realRurichan/Ruri-Passport/hardware/review/procurement-bound-status.md

# 当前采购绑定与样板输出状态

2026-09-27：完整源工程已导出至 manufacturing/latest/Ruri-Passport-RevA.epro2，当前 Gerber 已重新生成并一致性复核。PCB DRC 0；163 元件/354 引脚核对 0；57 BOM 组/144 CPL 位号匹配。原理图仍有三组供应商属性警告，已通过有效规格属性审核解释；不是零警告。

可提交裸板打样/工厂 DFM。全贴片供料未闭环：MIC1/J2/J3 当前为邮寄供料，麦克风自动替代料未核准。报价已知约 586.13/套仍缺项，非最低价。详细状态、限制和哈希见 ../manufacturing/latest/README.md、quote.md、manifest.json。
