realRurichan/Ruri-Passport/hardware/design/DISPLAY.md

# CL40BC264-40C 非触摸屏

用户指定 CL40BC264-40C 的 Without RTP 版本，替代此前所有候选。此前误传的 CL24CK229-18A 不采用。用户已接受 PCB 调整为 88 × 135 mm。

资料：用户提供的 `CL40BC264-40C_RTP&WithoutTP.rar` 中 `CL40BC264-40C_SPEC_V0 鸿讯电子.pdf`（第 3–9 页）及 `CL40BC264-40C接线图.pdf`。已核对非触摸机械图与四线 SPI 接线图；厂商原始文件和示例代码未复制入开源仓库。

2026-09-26 已在客户端保存 SPI 接线；PCB 尚未同步。原理图自定义符号仍有旧并口功能别名，连接以引脚编号及外部网络标签为准，别名整理待完成。

## 已确认参数

| 参数 | 数值 |
| --- | --- |
| 对角线 / 分辨率 | 4.0 英寸 / 320 × 480 |
| 驱动 IC | ILI9488 |
| 显示区 | 55.68 × 83.52 mm |
| 模组外形 | 60.88 × 94.57 mm |
| 非触摸版厚度 | 2.48 ± 0.15 mm，不含双面胶 |
| 排线 | 40 pin，0.5 mm 间距；端部宽 20.50 mm |
| 插入端厚度 | 0.30 ± 0.05 mm（FPC + PI） |
| 视角方向 | 12 点钟方向；不将其标为 IPS |
| 接口选择 | 四线 8 位 SPI，IM0=1、IM1=1、IM2=1 |
| VCC / IOVCC | 接线图采用 3.3 V；规格表正常工作上限 3.3 V，最终电源需计入容差 |
| 背光 | 8 颗白光 LED 并联；正向压降 2.9 / 3.1 / 3.3 V（最小/典型/最大） |

厚度不能用规格书第 3 页带 RTP 的 3.62 mm。现有 PCB 文档层 60.88 × 94.57 mm 包络可作近似包络，但未包含 FPC 折弯、连接器、装配公差和禁布区，不是最终机械封装。

## 40 pin 接口分配

| 屏幕针脚 | 屏幕信号 | 计划连接 |
| --- | --- | --- |
| 1–4 | XL / YU / XR / YD | 非触摸版本不连接 |
| 5、16、37 | GND | GND |
| 6 | IOVCC | 显示 I/O 电源，3V18_PERIPH |
| 7 | VCC | 显示电源，3V18_PERIPH |
| 8 | FMARK / TE | 本版暂不接，保留调试焊盘方向 |
| 9 | CS | LCD_CS_N / GPIO10 |
| 10 | RS | LCD_DC / GPIO9 |
| 11 | WR / SPI_SCL | LCD_SCK / GPIO8 |
| 12 | RD | 写入模式固定为高电平（IOVCC），不能悬空 |
| 13 | SPI_SDA | LCD_MOSI / GPIO16 |
| 14 | SPI_SDO | 不连接 |
| 15 | RESET | LCD_RESET_N，GPIO 扩展器控制；R5下拉，默认复位 |
| 17–24 | DB0–DB7 | 按厂商四线 SPI 图接 GND |
| 25–32 | DB8–DB15 | 按厂商四线 SPI 图接 GND |
| 33 | LEDA | 背光驱动输出，禁止直接接 MCU GPIO |
| 34–36 | LEDK | 三脚接同一背光阴极网络，经限流/驱动回路 |
| 38、39 | IM0、IM1 | IOVCC |
| 40 | IM2 | IOVCC |

GPIO43 分配 LCD_BL_PWM，用于控制背光驱动。Display.esch2 已绘制接口符号、模式配置、去耦、CS 上拉和 RESET 下拉。J1 已关联 FH12A-40S-0.5SH(55) 候选封装，Optics页已加入TLV9001+AO3400A恒流背光草稿，电源已加入Power页；不能当作制造网表。

## 背光和装配待办

- 第 5 页背光电流表的 160 / 200 mA 应结合原页列位置及供应商确认典型/最大值；暂按 200 mA 预留驱动和热预算，不据此承诺续航。
- 接线图用 3.3 V + 2.2 Ω 限流作示例。这不是恒流方案，不能据此保证电流；需按电源容差、LED 压降和实测选择 PWM 背光电路。
- 40 pin / 0.5 mm / 0.3 mm 只是连接器筛选条件。用户确认上接触；仍需复核锁扣方向、焊盘编号和最终折弯方向，再确定采购型号与 PCB 封装。
- 确认非触摸订货选项、单价与供应情况。未下单、未核价。

## J1 上接触座候选封装

型号 FH12A-40S-0.5SH(55)，原厂明确 FH12A 为上接触翻盖式。依据 [Hirose FH12 官方目录](https://www.hirose.com/product/document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) 本次下载版第 6、10 页建候选封装（目录版本页码可能不同）。

- 信号焊盘 40 个，0.5 mm 间距，0.30 × 1.30 mm，首末中心距 19.5 mm。
- 两个固定焊盘各 1.8 × 2.2 mm，横向中心 ±11.65 mm；相对信号焊盘中心线朝插入口方向 3.25 mm。固定焊盘不接信号。
- 以插入口朝 PCB 局部正 Y 的俯视图编号，1 脚置于局部 X=+9.75 mm；这是图纸解释，仍须对照独立料号图和实际排线复核，尚未生产签核。
- J1 暂放在 PCB (49,59) mm，位置随当前屏幕包络调整，用于验证折回排线方案，并非最终装配签核。
- 尚未完成钢网开口、阻焊、公差、丝印、装配间隙或 DRC 检查；嘉立创供料和价格未确认。不得把其他同针数连接器直接替换。
