realRurichan/Ruri-Passport/hardware/design/BATTERY.md

# 电池选型：VP505060 成品包候选

2026-09-26。首选孚赛能源 VCELL **VP505060** 的单节保护电池包，要求定制三线 NTC 与项目连接器。电芯规格方向已选定，成品包采购型号尚未冻结：公开页没有两只样品价格、起订量及该 NTC/线束配置的订单号。

## 厂家公开参数

| 项目 | VP505060 |
| --- | --- |
| 标称电压 / 容量 | 3.7 V / 2000 mAh，7.4 Wh |
| 充满电压 | 4.2 V |
| 最大持续放电 | 1.5C，即 3 A；不是峰值电流 |
| 最大充电电流 | 1C，即 2 A |
| 尺寸 | 厚 5.0 × 宽 50.5 × 长 62.5 mm，公开页称最大值、包含 PCM |
| 重量 | 约 34 g |
| 充电温度 | 0–45 °C |
| 定制选项 | 保护板、线材、插头、NTC |

依据：[VCELL 原厂产品页](https://www.vcellpower-battery.com/zh_cn/3.7v/505060-3-7v-2000mah-lithium-rechargeable-battery-with-pcm.html)。以上是公开参数，须以供应商确认的成品包规格书为准；网页没有证明任意保护板和插头版本均可连续输出 3 A。

## 与本项目的匹配

机械预留区为 x=6…71、y=40…100 mm，即 65×60 mm。把电池长边沿板 X 方向放置，62.5×50.5 mm 可放入该区域；拟定位 x=7.5…70、y=44…94.5 mm。这是平面包络筛查，NTC、绝缘胶、焊接折边及出线弯曲后的成品最大尺寸仍需供应商图纸；壳体需另外预留安装公差和厂家规定的膨胀空间，不能夹紧软包。三线约 80 mm 作为样品线长目标，最终长度按装配图确定。

现有功率分配以 3.18 V / 1.7 A、85%估算效率为基准，电池/VSYS=3.3 V时约2.14 A，若VSYS=2.8 V则约2.48 A（均含背光/IR约0.21 A）。3 A候选有设计余量，但效率、低电量压降和实际电流仍需样板验证。

**J3 已改为 3 A 接口：** JST S3B-XH-SM4-TB(LF)(SN)，采购编号 C161860，三针卧式贴片，XH 系列实际间距 **2.50 mm**。匹配线端外壳 XHP-3、端子 SXH-001T-P0.6；正负极功率线用 **22 AWG**，厂家 3 A 额定以该线径为条件。PH2.0 插头不兼容。针序按下方针号核对。PCB、原理图和 Gerber 已同步，严格 PCB DRC 为 0 错误；整机最大持续电流仍需样板验证。[JST XH 原厂规格](https://www.jst-mfg.com/product/pdf/eng/eXH.pdf)。

温度匹配尚需完成：候选电池规定充电 0–45 °C，BQ24074 配推荐 103AT-2 的原生窗口约 0–50 °C；不能据此认定完全匹配。电池成品包必须具备符合电芯要求的充电温度保护，或在量产前调整板端温度门限并验证。

## 成品包采购要求

- 1S 3.7 V、4.2 V充满、约2000 mAh；电芯、PCM、功率导线及最终插头均满足至少3 A连续能力，并提供过流保护阈值/延时。保护板过流触发电流不等于连续额定电流。
- 保护板具备过充、过放、过流、短路保护。采购必须包含保护板，不买裸电芯直接接板。
- 贴附电芯的 NTC：R25=10kΩ，优先103AT-2或经曲线核对的等效件，B25/85=3435K，阻值和B值公差按±1%要求；另一端接成品包P−。不能用第三根ID/数据线替代NTC。[SEMITEC参数](https://www.semitec-global.com.cn/products/thermistor_at/)、[TI BQ24074推荐103AT-2](https://www.ti.com/lit/ds/symlink/bq24074.pdf)。
- 当前电路的J3功能顺序：1=P+/VBAT，2=NTC/BAT_NTC，3=P−/GND。插头壳采用 XHP-3；以带针号的图纸核对，不以红白黑线色或所谓正反插头名称替代针号。
- 两只样品，供应商确认最小起订量、成品包全尺寸、放电曲线、样品单价、含税/运费及交期。尚无实际报价，不计入已核准整机成本。

## 未入选方向

普通仅写505060/2000mAh的通用电池不能自动等同VP505060；例如[亿莱505060](https://www.yilaipower.com/battery/fully-certified-505060-2000mah-3.7v-rechargeable-li-po-battery.html)公开持续放电仅1C（2 A），达不到当前3 A采购目标。103450通常更厚，本项目优先5 mm级软包，避免增加机身厚度。

## 可复制给商家的询问文本（尚未发送）

需要2只VP505060单节3.7V/2000mAh保护锂聚合物电池，4.2V充满。要求电芯、保护板和线束连续放电≥3A，支持约0.5A充电，带贴附电芯的10kΩ±1%、B25/85=3435K±1% NTC，NTC另一端接保护输出P−。请提供成品包规格书、持续放电测试条件、保护阈值/延时、带NTC与线束的最大尺寸、起订量、2只样品单价和运费。线长暂按80mm，插头采用XHP-3，功率导线22AWG，端子SXH-001T-P0.6；1=P+、2=NTC、3=P−，按针号图确认后制作。不要用3.8V/4.35V高压电芯或两线版本替代。
