realRurichan/Ruri-Passport/hardware/design/MECHANICAL.md

# 88×135mm 布局草稿

2026-09-26用户同意板长从125mm增加至135mm，以天线净空和可用性为优先。下表为PCB左下角原点，单位mm，正Y向上。元件仍在布局，不是机械签核。

| 对象 | 拟定位置/外形 | 状态 |
| --- | --- | --- |
| PCB | x=0…88，y=0…135 | 原生板框已更新、读回确认 |
| 非触摸屏 | x=13.56…74.44，y=38.5…133.07 | 60.88×94.57；未计FPC与装配公差 |
| 后侧电池 | x=6…71，y=40…100 | VP505060 成品包候选，62.5×50.5×5 mm；三线NTC、线束、壳体余量待核准，见 BATTERY.md |
| ESP模组 | x约4…22，y约0…25.5，天线朝下 | 原生封装外形；需整机RF复核 |
| Wi-Fi天线周边 | 板内x=0…37，y=0…约21 | 已生成四铜层禁止导线、填充和铺铜区域，排除模组自身屏蔽/焊盘区 |
| NFC板载线圈 | x=53…87，y=1…25 | 34×24、4匝、0.4线宽/0.3间距初值；铜线与馈线已画入，整机调谐待完成 |
| 五向键中心 | UP(42,31)，DOWN(42,17)，LEFT(35,24)，RIGHT(49,24)，OK(42,24) | 7mm中心距，OK开关旋转90°避让焊盘；UP开关本体距屏幕外框约4.95mm。键帽外沿和装配公差待核查 |
| USB-C | 下边缘，中心x=44 | 座体/开口与焊盘待核对 |
| microSD | 右边缘，中心y约73 | 卡插拔包络待核对 |
| POWER | 右边缘，y约89 | 须检查伸出量与壳体行程 |
| M2 固定孔 | H1(3,132)、H2(84.5,132)、H3(3.5,38)、H4(84.5,50) | Ø2.2mm 非金属化孔，四层铜箔避让 Ø5.2mm；螺柱外径≤4.5mm，螺丝头直径≤4mm |

屏幕金属与NFC线圈上缘的平面间隔为13.5mm；这一间隔不能证明射频性能。按键、USB壳、电池线、螺丝柱和外壳金属也需纳入调谐。

屏下器件、背面电池、FPC折回、连接器插拔和声孔都未完成高度/实体干涉验证。J1暂移至(49,59)，仅随屏幕包络上移，FPC端部基准及上接触方向仍须确认，不能直接据此开外壳。

四铜层已启用。暂定单面SMT以控制贴片成本；最终叠层、板厚、阻抗和报价在布线及制造核查中落实。本尺寸不按10×10cm免费板预算。

MIC1 为板载底部声孔麦克风，库中有约 Ø0.4mm 通声孔；需在最终钻孔文件及外壳中确认畅通。扬声器采用 J5 外接 8Ω/≥1W 单元，实体和线束仍待选定。

后壳扬声器暂按 Ø28×5mm 安装包络，中心 (30,117)，位于电池占位上方；这只是装配空间预留，不代表已选定或核价的扬声器。麦克风通声孔中心约 (82.786,110)，后壳需单独声孔或声道，避免电池、泡棉和螺柱遮挡。

2026-09-26补充：用户要求扬声器以便宜、能响为主。候选兴华鑫20MM-8Ω1W-L60MM（C49246973），Ø20×4.2mm，保持现有较大包络；尚须配好PH2.0双针成品线束并确认国内两件价格，未冻结采购。电池仍未定型号，约2000mAh、保护板及NTC要求不变；见[审核与报价](../review/assembly-quote-20260926.md)。

用户于 2026-09-26 明确要求预留外壳固定孔。下方两个固定孔采用错位布局，避开 Wi-Fi/NFC 天线和电池占位；外壳底边还需绝缘支撑台阶，承接按键和 USB 插拔力。固定孔与螺柱区域位于屏幕外形左右两侧。H1 与红外接收器较近，按 Ø5.2mm 预留包络平面筛查，正式外壳设计仍须核对器件高度和装配公差。权威坐标见 `mounting-holes.json`。
