realRurichan/Ruri-Passport/hardware/review/usb-footprint-correction-20260926.md

# GCT USB4105 封装修正依据

2026-09-26。对原厂 USB4105 Rev B1 两页尺寸图与原生封装进行一次独立只读比较；随后按厂家推荐铜图修正。此记录不等同于生产放行。

- 原厂图：<https://datasheet.octopart.com/USB4105-GF-A-060-GCT-datasheet-192318489.pdf>。图纸覆盖 USB4105 系列的 shell stake 长度选项。
- 原型号 USB4105-GF-A 对应供应商候选 [C3020560](https://www.lcsc.com/product-detail/C3020560.html)，尚未确认国内贴片库与订单价格。
- PCB 以 USB 中心线 x=44 mm、板边 y=0 为基准，J2 原点 (44,4.973) mm。
- 16 个逻辑 SMD pad 保持原引脚/网络，宽 0.30、长 1.15、中心 y=7.355 mm；左右电源/地相邻 pad 边缘相接，等价于厂家四个 0.60 mm 合并铜区。
- 两定位孔恢复为 (41.11,6.28)、(46.89,6.28) mm，孔径 0.65 mm。没有缩孔或删除定位孔。
- 四个外壳槽 x=39.68/48.32 mm；前排 y=2.60，孔 0.60×1.40、铜 1.00×1.80；后排 y=6.78，孔 0.60×1.70、铜 1.00×2.10 mm。槽和铜均为纵向长圆。
- 手工锡膏图形同步目标铜图；厂家图的 solder area 不是已确认的钢网开孔/锡量规范，最终钢网仍须生产审核。
- 默认 stake 长度 S=0.95±0.15 mm 不是板厚要求；本图没有给出板厚上限/下限。短脚 PTH 的实际贴片/焊接工艺尚待确认。

修正后定位孔与最近焊盘的名义净距为 `hypot(0.01,0.50)-0.325 = 0.175100 mm`，大于现有 6 mil 电气间距规则，仍小于嘉立创常规 NPTH 0.20 mm 避铜要求。保留原规则，不设忽略项。最终钻孔、铜层和钢网导出核对及嘉立创 DFM 接受记录完成前，USB-1 制造项仍未关闭。

廉价候选 SHOU HAN TYPE-C16PIN2MD(073) / C2765186 未采用：库与厂家孔、焊盘及槽尺寸不一致，图纸另推荐 0.80 mm PCB；不能以其价格直接替换当前 1.6 mm 板方案。
