realRurichan/Ruri-Passport/hardware/review/power-review-20260926.md

# Power 方案独立审查

只读、单轮，2026-09-26。未读取旧 review；未改 EDA、源脚本或工程。检查 add_power.py、Power.esch2，并交叉读取 Controls 的实际网络；阅读 TI/ADI 原始资料。没有运行原生 ERC、测量实板或验证封装尺寸，因此以下是电气方案和源文件审查，不是放行结论。

**FIX FIRST：P1、P2、P4。P3 必须明确实现或记录为首版限制；已知 ESD/输入保护缺口仍未关闭。**

## P1 — SERIOUS：LTC2950 的 SD 安全关机时间不能靠 OFFT 延长

实际 U5=LTC2950CTS8-1，C17=330nF。INT 经 TCA9535 P06 通知主控；PB 没有更早的独立检测。约2.15秒按键时间过去后才产生 INT，此后自动切电时间最短只有800ms（典型1024ms）。软件真正拿到中断后还要付出 I²C、调度、停止应用、文件系统同步与卡内部忙时间。没有任何已验证的最长处理时间。任意 SD 卡和用户应用下，不能把它称为保证安全关机。增加 C17 只推迟 INT，不增加最后窗口。[ADI LTC2950，p3、p8–11](https://www.analog.com/media/en/technical-documentation/data-sheets/295012fd.pdf)

最小硬件修复：采用 **LTC2954-1 的 TS8**，针号1–8功能对应，7脚改名 PDT；其 INT 可在按下约32ms时报出，持续长按才由 PDT 强制切断。C17可改1µF，形成约6.4秒强制关机时间；核实容差后的最短时间。普通按键请求由系统完成同步/等待卡非忙，再通过 KILL 切断。强制关机仍要明确可损坏未完成写入，不能承诺任意卡无损。应重新核对精确料号、库与供货，不能仅在 BOM 中改字符串。[ADI LTC2954，p2、p9](https://www.analog.com/media/en/technical-documentation/data-sheets/2954fb.pdf)

## P2 — SERIOUS：没有电池低电量预警路径，保护板切断不是正常关机策略

实际可见信号只有 CHG、USB_PGOOD、PWR_INT；没有 VBAT 分压到 ADC、外部电量计或低电压比较器。TPS63802 会维持3V18直到低电压/电流条件无法满足；测3V18或其PG不能提前代表电芯余量。最终可能是电池保护板突然切断，SD 正在写入。电池保护器的实际门限和恢复条件还未确定。

最小修复：加一个独立于稳压输出判断的电池低电压监测，可用 I²C 电量计/ADC，或阈值与迟滞明确的低功耗比较器，输出给 TCA9535 剩余输入。设正常关机阈值高于保护阈值，并按电池压降与实际最大负载验证余量。不要把 BAT_NTC 复用成电压采样；不要仅给 KILL 加电池分压立即断电，这仍不提供SD清理时间。[TPS63802 UVLO 参数](https://www.ti.com/lit/ds/symlink/tps63802.pdf)

## P3 — SERIOUS 功能/启动风险：关机状态不是500mA充电，USB空电池启动尚无预算

实际 EN1/EN2 来自切换电源域 TCA9535，外部100k下拉。关闭主轨时两者低，选择USB100；R22的500mA设定无法越过输入限流。由2000mAh/100mA算出的理想下限已经20小时，尚未算恒压阶段和负载。主控只有成功启动后才能切换500mA，电池缺失/保护断开时的启动能量没有验证。100mA×4.4V 即便假设90%效率，也仅约125mA@3.18V，且还未扣充电。不能以“USB-C+500mA充电”概括关机体验。[BQ24074，表7-2及电源通路](https://www.ti.com/lit/ds/symlink/bq24074.pdf)

最小方案选择：RevA明确接受关机100mA慢充，低负载启动并尽早合法切换限流；验证无电池、空电池与ROM下载模式。若要求关机也能自动快充，需要始终供电的USB来源检测/限流控制逻辑，识别允许电流后再控制EN，不能简单把EN1上拉为500mA。固件枚举、复位和挂起策略也必须覆盖，不能只在应用启动时写一次。

## P4 — SERIOUS：生成脚本与当前图纸的网络已分叉

add_power.py 仍向MODE、反馈分压上端、电源电容、KILL/INT上拉写 `3V3`，图纸中实际已是 `3V18`。add_controls.py 仍写 IOX_SPARE4/5、USB_PRESENT，实际 Controls 图纸已写 CHG_EN1/2、USB_PGOOD_N。读过 schematic_sheet.py，没有发现对此的统一转换。这不是现有图纸已经断线的证据，而是重新生成会撤销修复的确定风险。

最小修复：统一源脚本中的实际网名及引脚映射；以一个主轨常量定义3V18。新脚本输出目录做网名清单检查，禁止遗留3V3/旧控制信号。不要在活跃EDA打开的项目上直接覆盖生成来试验。

## 已核对正确的内容

- U3 BQ24074 RGT、U4 TPS63802 DLA、U5 LTC2950 TS8 的已画针号/功能与厂家图一致。BQ24074热焊盘同VSS接地、BAT2/3并联、OUT10/11并联正确；TMR/ITERM悬空有明确厂家定义。NTC为103AT-2有TI参考支持；仍须锁定实际电芯允许温区和插头线序。[BQ24074 p7–9、p34–35](https://www.ti.com/lit/ds/symlink/bq24074.pdf)
- R23=3.48kΩ±1%，按KILIM最大值计算上界1720/(3480×0.99)=499.25mA，没有凭此允许大于500mA。R22的500mA是标称设定，实际还受输入总功率限制。
- LTC2950-1 的 EN 可由R29上拉VSYS，KILL由切换主轨上拉并由GPIO44开漏拉低，极性正确；无需让主控在启动期间主动迅速拉高KILL。[ADI LTC2950](https://www.analog.com/media/en/technical-documentation/data-sheets/295012fd.pdf)
- TPS63802针号正确、MODE接主轨为强制PWM、53.6k/10k得到标称3.18V。含±1%反馈、±0.1%分压、100nA偏流的保守直流上界约3.223V；离屏幕3.3V只剩约77mV瞬态余量，必须实测，不能称已验证。C12有效输入电容需≥4µF，输出需≥7µF；C12–14目前未锁定制造料号和DC偏压曲线。L1 XFL4015-471在TI推荐表中，本审查没有发现它必须替换的证据。[TI TPS63802 p5–6、p18–19](https://www.ti.com/lit/ds/symlink/tps63802.pdf)

## 待验证，不作为已经发生的故障

- USB输入防护和接口ESD尚未画，这是已知未完成工作，不应凭IC内部HBM额定当作系统ESD验证。
- 3V18全系统峰值负载、BQ24074热设计、短路恢复、空电池启动和关机残余电压没有实测。尤其前屏背板和电池会影响散热。
- BQ24074内部充电定时会随若干限流工况动态变慢；未证明“100mA慢充必定5小时超时”，故不作此断言。
- 这次没有原生导出最终网表，没有宣称所有视觉线段都被EDA识别为连接；封装焊盘编号、USB插座机械脚编号与丝印极性仍应在网表/封装阶段核对。
