realRurichan/Ruri-Passport/hardware/review/usb-slot-review-20260926.md

# J2 USB 定位孔 DRC 有界审查

2026-09-26；只读、一次审查。范围仅为 J2_B1/B12 到 e62/e63 的两项 5.7 mil 间距错误。未修改工程、封装、规则或 GUI。终止条件：独立复算这两项、对照 GCT 原图和嘉立创能力，给出修正路径或明确未解决项。

**结论：FIX FIRST: USB-1。不能作为已证明的 DRC 特例忽略，也不能通过把全局 6 mil 降为 5.7 mil 解决。存在可复现的封装几何偏差；即使完全恢复厂家推荐图，也仍需处理嘉立创的孔边避铜要求。**

## USB-1 / SERIOUS：定位孔与焊盘间距不足

审查文件：`hardware/eda/Ruri-Passport-RevA/pcb/Mainboard.epcb2`，读取时 SHA256 `b0bde020a13fd38d02f98c9aa228909e2b7e01cc48a1f64c89d6f62c3db9a0d2`。J2 实例 `9902f32e4ca8c9c7`，封装 `4305e825ef9fa5d6`。该库内部名称是 `TYPE-C-SMD_SBC-160S1A-20-S412`，并非已经核准的 GCT 专用封装。

独立读取原生记录得到（以下坐标均为封装局部坐标、单位 mm）：

| 项目 | B1 / e62 | B12 / e63 |
|---|---:|---:|
| SMD 焊盘中心 x | +3.050032 | −3.050032 |
| SMD 焊盘中心 y | 2.372106 | 2.372106 |
| 铜焊盘宽 × 长 | 0.2999994 × 1.1500104 | 同左 |
| 定位孔中心 x | +2.890012 | −2.890012 |
| 定位孔中心 y | 1.327150 | 1.327150 |
| 孔半径 | 0.324993 | 0.324993 |
| 独立计算净距 | 0.1450646 | 0.1450646 |

净距为圆到矩形的最短距离：`hypot(0.0100203, 0.4699508) − 0.324993 = 0.1450646 mm = 5.7112 mil`。可复现原生 DRC 的 5.7 mil；焊盘偏移字段只有约 0.0003 mm，不能解释或消除该差距。

e62/e63 的库源记录是 layer 12 上 `FILL/CIRCLE`，原生 DRC 以 SLOTREGION 报告。它们实际表示两个约 Ø0.65 mm 的塑胶定位柱孔，**不是**四个接 GND 的外壳镀铜槽。B1/B12 是 GND 不构成孔边工艺豁免。

### GCT 原图交叉检查

核对了 [GCT USB4105 产品页](https://gct.co/connector/usb4105)，并视觉检查了 GCT 自己出具的 USB4105 drawing Rev B1、2022-12-28、第 1 页（[Octopart 原厂图镜像](https://datasheet.octopart.com/USB4105-GF-A-060-GCT-datasheet-192318489.pdf)）。官网下载端点返回 403，所以本次没有宣称核到了更新的官方图修订。

图中推荐定位孔 Ø0.65、孔距 5.78；合并 GND 焊盘宽 0.60、长度 1.15；定位孔基准尺寸 3.68、焊盘靠孔边基准尺寸 4.18。因此厂家推荐的纵向孔中心到焊盘边距离为 **0.50 mm**。当前模型只有 **0.46995 mm**，约少 0.03005 mm。厂家推荐图的名义最短净距约 `hypot(0.01, 0.50) − 0.325 = 0.17510 mm`，可通过现有 6 mil（0.1524 mm）规则；当前兼容库不能直接视为与该图等价。

这不是“厂家推荐图天然就是 5.7 mil”的特例。另一方面，0.1751 mm 也不能自动视为适合嘉立创所有加工选项。

### 嘉立创制造风险

[嘉立创国内 FR4 工艺能力](https://www.jlc.com/portal/vtechnology.html)列出：无铜孔周围会掏空 0.2 mm 的焊盘或铜面；走线/焊盘距锣槽要求 ≥0.2 mm。[JLCPCB FR4 能力表](https://jlcpcb.com/capabilities/Capab)也给出 NPTH-to-track 0.2 mm。这里不能套用柔性板或普通铜线间距规则。

若按现状制板，定位孔附近的焊盘跟部可能被生产避铜修改，缩小焊接面积；有孔位及钻孔尺寸公差时，不能把名义未相交等同于有足够工艺余量。没有拿到针对本项目的生产稿确认，不能证明实际一定失败，也不能标记制造通过。

## 最小修正路径

1. 保留定位孔中心及 Ø0.65；不要为消除 DRC 擅自移孔、缩孔或删除塑胶柱孔。按 GCT 图重新核准 USB 专用封装，首先消除约 0.030 mm 的孔到焊盘位置偏差，并核对合并的 A1/B12、A12/B1 铜焊盘及对应钢网开口。
2. 仍需解决 0.1751 mm 与常规 0.2 mm 避铜之间的差距。优先方案是在不移动孔的前提下，仅调整焊盘靠孔的跟部，并同步钢网，使实测净距至少 0.20 mm，宜留到 0.22 mm；以 GCT 推荐几何为起点，跟部需再退约 0.025 mm / 0.045 mm。**这只是零新增元件的候选修正，实施前须核对实际焊脚接触区、落点和装配公差，不能无条件截短焊盘。**
3. 如坚持厂家原始 0.1751 mm，必须有本次嘉立创 DFM/生产稿对这一局部孔边几何的接受记录，才可设置局部例外；不能降低全局孔到铜规则。没有这样的记录时，本项保持未解决。
4. 修正后原生 DRC 必须复测，并在导出钻孔、顶层铜、钢网上独立确认两个孔的位置、孔径及净距；只让原生计数归零还不足以关闭本项。

不需要更换芯片或增加贴片料种；是否仍选 GCT 插座及其具体料号由后续 BOM 成本审查决定。本审查没有取得全套加工报价。

## 已核实与未解决边界

- 已核实：两个报错对称且确实为定位孔；独立几何复现 5.7 mil；当前库与原厂推荐图在上述距离上有约 0.030 mm 偏差；不是不同电气网短路问题。
- 未解决：最新供货修订与当前图的一致性；最终焊脚/修改焊盘的装配容差；国内下单实际生产稿是否接受 <0.2 mm；当前圆形挖空在最终 NPTH 钻孔文件中的表达。本次没有导出或修改来验证这些项目。
- 没有扩大审查到其他 USB 焊盘、外壳槽孔、连接器机械强度或全板 DRC；不据此宣称整个 USB 封装或 PCB 合格。

一次审查结束。
