realRurichan/Ruri-Passport/hardware/review/jlc-dfm-stock-20260927/disposition.md

# 官方 DFM 核对记录（未完成放行）

最终源工程 SHA256 dc4defeafbaf8d82c364678edf59d2545d8c48548a765dd1aaf4b7e25f9bf841；最终 Gerber SHA256 30338a62356b38e63e04a07f3bd59488a82defca9ee8c8db4cb2b63fbafdfdb6。
最终 Gerber 官方任务 DFMP2609270143；旧 DFMP2609270089 报告仅保留为修改前证据，不能代表最终 SMT 检查。

已经确认：
- 最终原生 141 项 PCB DRC 为零；新鲜网表 163 元件、354 项引脚核对为零；57 组 BOM/144 位号、最终 CPL 位置/旋转/面别和采购料号一致，NFC 16 段与 Gerber 一致。
- 相比现货替换检查点，仅 U3 向右 0.06 mm、位号随动、3 段 VBUS 短线和原生重新铺铜改变；失败的大位移试验已经撤销，五向键位置未变。见 stock-spacing-source-diff-20260927.json。
- 旧 SMT 自动对齐后 PIN 脚无焊盘为零；U3/SW2 的实际最小器件间距原为约 0.15 mm，最终微移增加间距，最终官方模型结果仍待新任务返回。

制造能力与报警阈值的区别：
- 嘉立创现行多层工艺表允许金属槽宽 ≥0.35 mm、长 ≥0.70 mm；J2 0.6×1.4/1.7 mm 槽在范围内。软件 0.6 mm“危险”不是本叠层的能力判定。
- 普通多层过孔铜径至少比孔径大 0.10 mm，推荐更大。本板常用 0.508/0.3048 mm；NFC 末端 0.6/0.3 mm。软件将方形 0.4 mm 焊盘与末端过孔分别计数，不能把插件孔环阈值套在过孔上。
- 全局最小线距官方解析 0.11 mm，在多层 1 oz 的 0.09 mm 能力内。0.0872 mm 近焊盘对经原生定位均为 GND，不能因此判为不同信号短路；装配阻焊风险仍单独核对。
- 板边器件 U1/J4/IR1/J3 告警需配套至少 5 mm SMT 工艺边；采用嘉立创帮拼板加工艺边，生产文件仍保持单板坐标，不手动偏移 CPL。天线侧工艺边分板后必须移除，不作为最终天线周围铜结构。

来源：[现行工艺能力](https://www.jlc.com/portal/vtechnology.html)、[工艺边和定位](https://www.jlc.com/portal/q6i22406.html)、[嘉立创帮拼板工艺边](https://www.jlc.com/portal/q2i32719.html)。

仍需完成：最新 SMT 模型匹配及碰撞复核；U4/U7 地过孔与焊盘开窗/钢网交互；USB 0.1751 mm NPTH 最近铜间距；裸线头 3 个及丝印/阻焊提示定位。不能称官方 DFM 零报警，也不能把上述待办自动核销。

## 15:xx 最新清理版（最终上传待完成）
当前生产源SHA256 0a911450f8979d6926be05e46b2004ed8b1dd404c2153bfe844008591b480f9c；Gerber SHA256 6937f92b96ef50de8d55bfd96bb5f2b90ed818afa35cb09e73a90c045109408e。DFMP2609270128/official-after-q1-report.pdf 仅对应USB退让、线尾清理之前的版本：碰撞0危险/1警告，器件距离0危险/1警告，PIN脚无焊盘0；不得称该报告验证了本次最终铜形。
USB NPTH已修：四GND焊盘孔侧退0.05mm、两配对钢网开孔同步，其他12接触焊盘/4固定槽保持；独立解析四层Gerber最小净空0.209883mm，详final-clean-usb-clearance-20260927.json。三条单端线尾e983(3V18,Inner2)、e2625(USB_CC1,Top)、e3079(USB_CC1,Inner1)已原生删除，重铺铜保存；原生strict[]、GUI141项0。不能把删除候选数量直接当官方裸线头统计已经归零。
热焊盘过孔仍非树脂塞孔工艺；需完成U4/U7开窗/钢网相交风险判定、厂家模型PIN边界与真实厂家land pattern比对及最终DFM重新分析。绿油/丝印工厂能力阈值不能无条件豁免全部警报。边沿装配必须至少5mm工艺边。
当前在线文件上传窗口不提交：反复路径输入变句号，文件已选中但打开控件无效果，CUA连接恢复仍无效；已请用户手动点击打开，上传的是Gerber，不涉及购买付款。其余本地制造检查和最新生产文件已完成，完整全贴片放行仍未宣布。
