realRurichan/Ruri-Passport/hardware/mechanical/screen-fit-check-1to1.pdf

# 屏幕与主板装配核对 · 正面坐标

Ruri Passport · CL40BC264-40C 非触摸版 · 2026-09-26

A4 / 实际大小 / 100%打印；关闭“适合页面”。先量标尺，再核对实物。

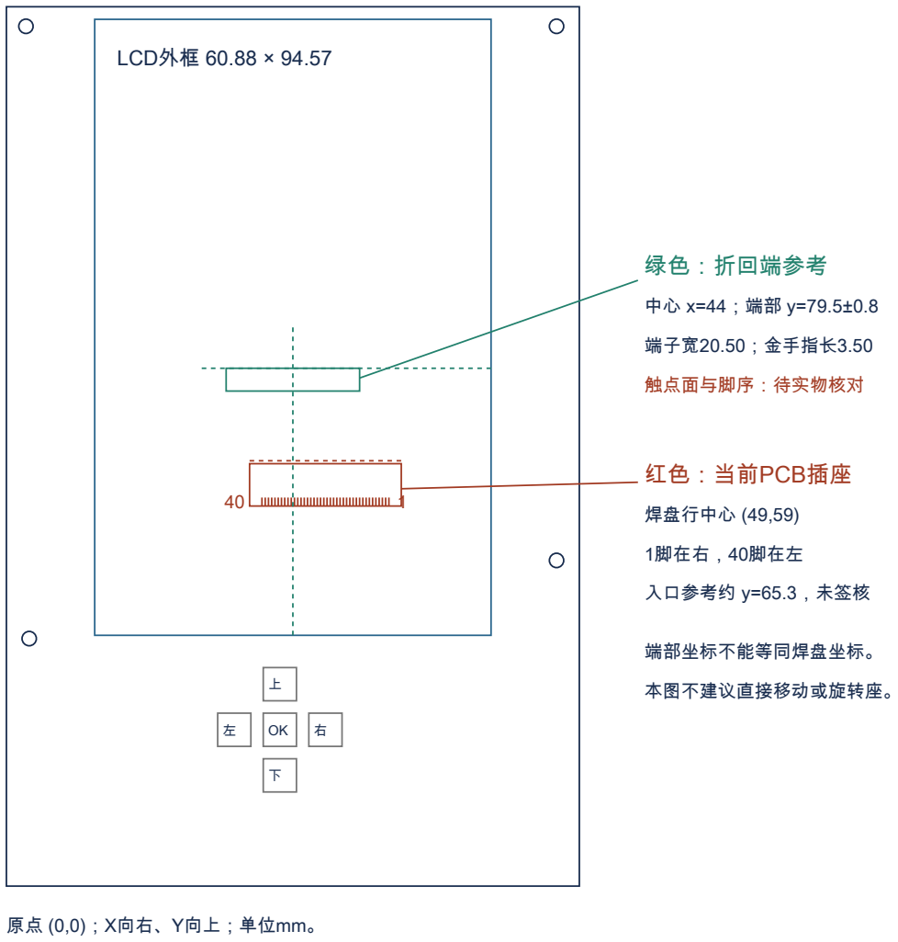
[picture p1: figure]
LCD外框 60.88 × 94.57; 绿色：折回端参考; 端子宽20.50；金手指长3.50; 触点面与脚序：待实物核对; 红色：当前PCB插座; 焊盘行中心 (49,59); 1脚在右，40脚在左; 入口参考约 y=65.3，未签核; 端部坐标不能等同焊盘坐标。; 本图不建议直接移动或旋转座。; 原点 (0,0)；X向右、Y向上；单位mm。

1/2 · 原创核对图 CERN-OHL-S-2.0 · 非制造放行图；不得据此加工外壳。

蓝框：屏幕外形；黑框：88 × 135 PCB；圆圈：现有M2孔。

将屏幕放在蓝框内，排线按自然弯曲路径放置，勿强扭或压死折线。

这条线必须实测为 50 mm

记录：触点朝屏背 / 朝PCB？

插头能否平直进入并锁紧？

屏背到PCB间隙：______ mm

实际端部中心：x____ / y____

# 屏幕排线核对 · 展开参考

Ruri Passport · CL40BC264-40C 非触摸版 · 2026-09-26

A4 / 实际大小 / 100%打印；关闭“适合页面”。先量标尺，再核对实物。

2/2 · 原创核对图 CERN-OHL-S-2.0 · 非制造放行图；不得据此加工外壳。

屏幕正面 / 显示侧

1 | 40

42.70

左边到端子左边20.19

端子宽20.50

厂家展开图中的1/40脚方向

仅对应左图观察方向。

端子间距：0.50 mm

首末触点中心距：19.50 mm

排线端厚度：0.30±0.05 mm

虚线只表示宽度/投影参考，

不是完整FPC外形，不能裁切成

最终排线或推断弯曲半径。

到货后用笔标明金手指裸露面；

绕到屏背后，重新核对1/40。

连接器：暂用 FH12A-40S-0.5SH(55)，上接触、40pin、0.5mm。

闭锁高2.0mm，开启约3.6mm；需先插排线、锁扣，再固定屏幕。

打印纸不能验证触点接触、折弯寿命或高度干涉；仍需实物试装。

这条线必须实测为 50 mm

尺寸依据：用户CL40BC264-40C非触摸规格第6页；本图为重新绘制的核对辅助图。
