realRurichan/Ruri-Passport/hardware/eda/README.md

# 当前硬件工程入口

2026-09-27 首板源工程以 ../manufacturing/latest/Ruri-Passport-RevA.epro2 为准；可导入嘉立创 EDA 专业版，完整保留 NFC 局部桥接铜。制造包状态见 ../manufacturing/latest/README.md。

proposals/Ruri-Passport-Procurement-Bound.eprj2 是当前客户端工作工程，配套同名 epro2 为当前导出。其它目录及旧 epro 是历史草稿/实验，不作为本次生产来源。旧 epro 不能完整保留 NFC 桥接铜，不可据旧格式直接再生成投产文件。
