realRurichan/Ruri-Passport/hardware/review/schematic-drc-20260927.txt

最新原生原理图 DRC 核对：2026-09-27 01:06:50
来源：嘉立创 EDA 专业版 sch_run_drc(strict=true) 返回及原生 DRC 面板。
此文件为读回结果摘要，并非原生导出日志全文。

致命错误：0
错误：0
警告：1
元件的属性与供应商编号不匹配，建议使用器件标准化：U2($4I2)

信息：J1 的 MP1、MP2 焊盘没有对应原理图引脚（连接器机械固定焊盘）。

其他复验：185元件，408项厂商引脚连接检查通过；36个有意NC标记已在冷启动后的epro中识别；C4/C49不贴装设置通过原生ENET复验。
本结果不代表PCB布线、器件工作条件或整机功能验证通过。
