realRurichan/Ruri-Passport/hardware/review/jlc-dfm-stock-20260927/official-after-q1-report.pdf

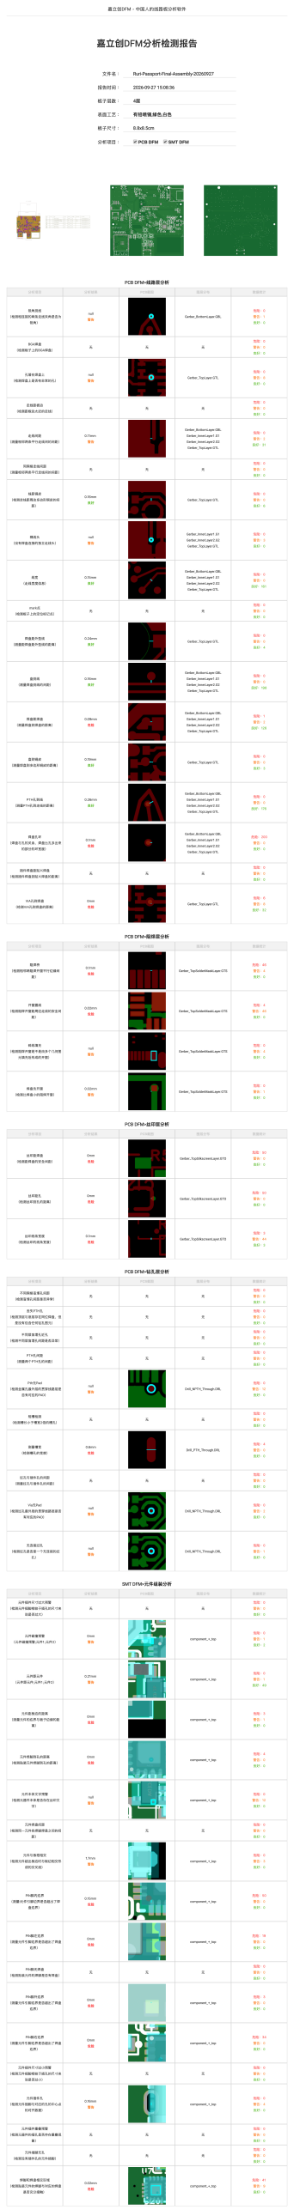
[picture p2: page 1]
